philippderroole/RockeyHockey2026/UIServer/resources/gifs/dog.gif

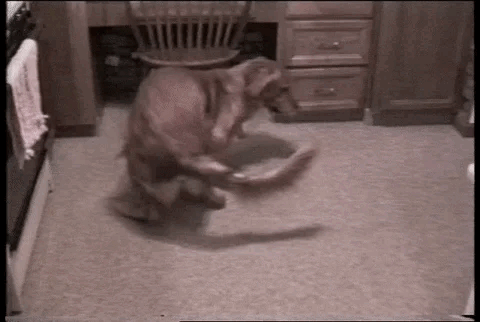
UIServer/resources/gifs/dog.gif
