philippderroole/RockeyHockey2026/CAD/Solidworks/RH_Baugr_Pulley_with_Rail_35mm_X_Axis.SLDASM

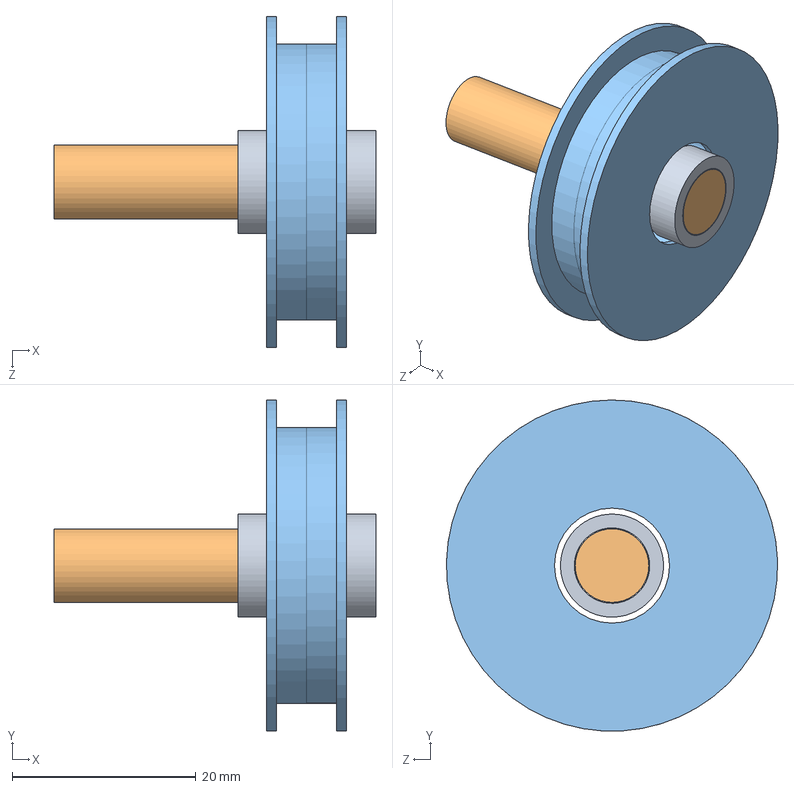
[picture p7: CAD file, 2023-06-27]
CAD/Solidworks/RH_Baugr_Pulley_with_Rail_35mm_X_Axis.SLDASM
35.0 x 36.0 x 36.0 mm
RH_Pulley_36mm_608_GT2_6mm x 2
RH_Rail_8mm_35mm
RH_Spacer_4mm x 2
