philippderroole/RockeyHockey2026/CAD/Solidworks/RH_Baugr_Pulley_with_Rail_24mm_Y_Axis.SLDASM

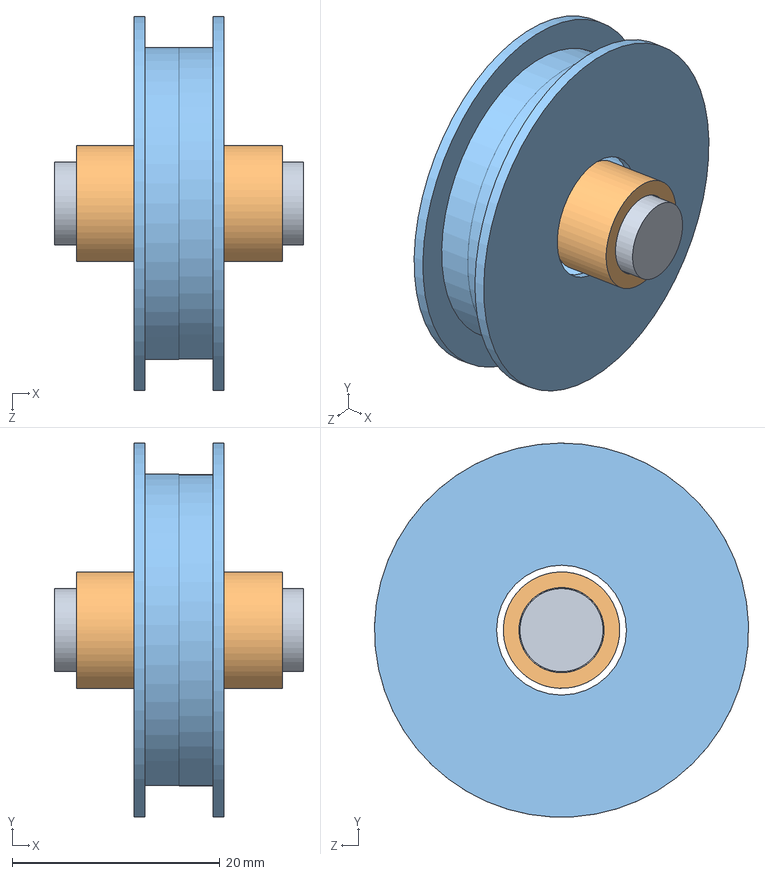
[picture p8: CAD file, 2023-06-27]
CAD/Solidworks/RH_Baugr_Pulley_with_Rail_24mm_Y_Axis.SLDASM
24.0 x 36.0 x 36.0 mm
RH_Pulley_36mm_608_GT2_6mm x 2
RH_Spacer_6_5mm x 2
RH_Rail_8mm_24mm
