philippderroole/RockeyHockey2026/CAD/Solidworks/Rocky_Hockey_Full_Assembly.SLDASM

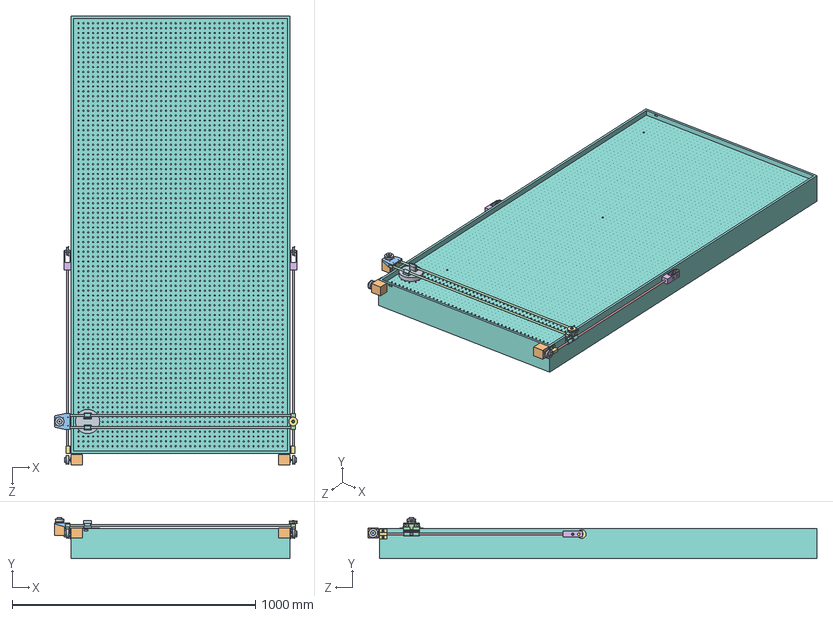
[picture p11: CAD file, 2023-06-27]
CAD/Solidworks/Rocky_Hockey_Full_Assembly.SLDASM
1000.4 x 168.8 x 1847.3 mm
RH_Tisch
RH_Rail_Stopper x 2
RH_Rail_Stopper_with_Pulley x 2
RH_Rail_8mm_770mm x 2
RH_Y_Carriage x 2
RH_Y_Carriage_Motor_Mount
RH_Nema17_Motor x 3
RH_35mm_Riemenscheibe x 3
RH_Bushing_8mm_15mm x 6
RH_Pulley_36mm_608_GT2_6mm x 6
RH_Spacer_6_5mm x 4
RH_Rail_8mm_24mm x 2
RH_Rail_8mm_944_85mm x 2
RH_Rail_8mm_35mm
RH_Spacer_4mm x 2
RH_X_Carriage_Bushings
