philippderroole/RockeyHockey2026/CAD/Solidworks/RH_Nema17_Motor.SLDPRT

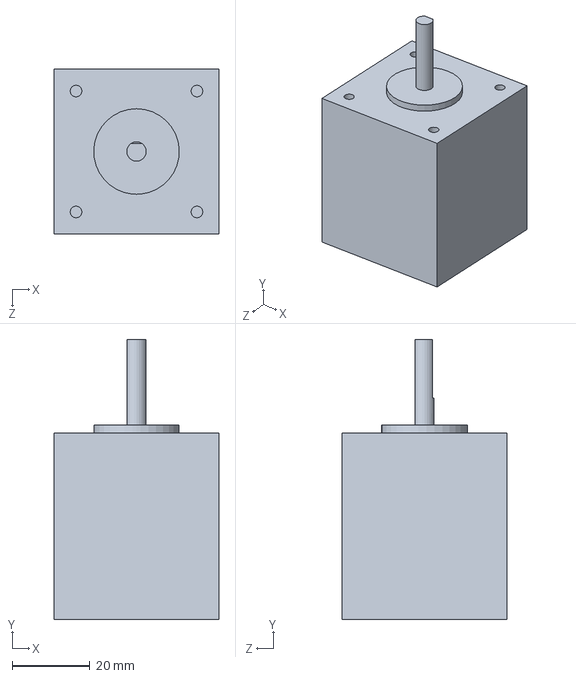
[picture p23: CAD file, 2023-06-27]
CAD/Solidworks/RH_Nema17_Motor.SLDPRT
42.3 x 72.0 x 42.3 mm
