philippderroole/RockeyHockey2026/CAD/STL/X_Carriage_Bushings.STL

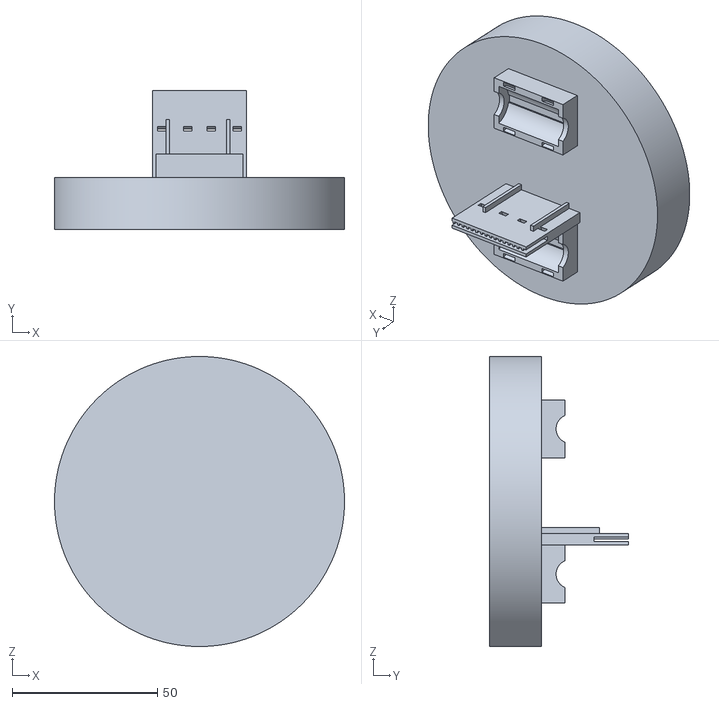
[picture p24: CAD file, 2023-06-27]
CAD/STL/X_Carriage_Bushings.STL
100.0 x 48.0 x 100.0
