philippderroole/RockeyHockey2026/CAD/Solidworks/RH_Rail_Stopper.SLDPRT

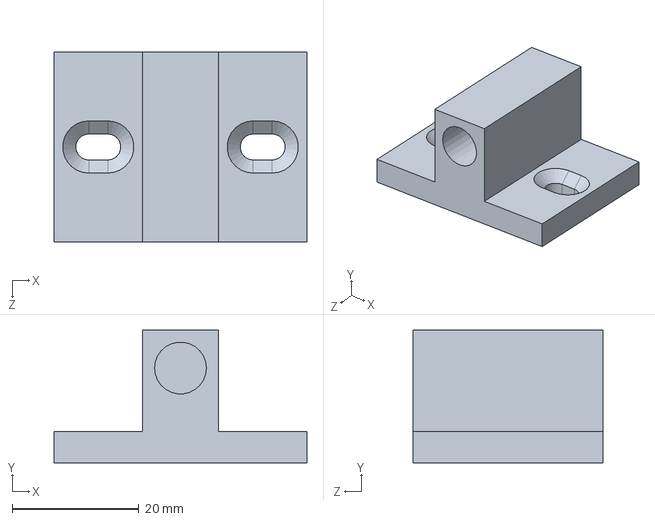
[picture p25: CAD file, 2023-06-27]
CAD/Solidworks/RH_Rail_Stopper.SLDPRT
40.0 x 21.0 x 30.0 mm
