philippderroole/RockeyHockey2026/CAD/STL/Pulley_48_Teeth_GT2_6mm.STL

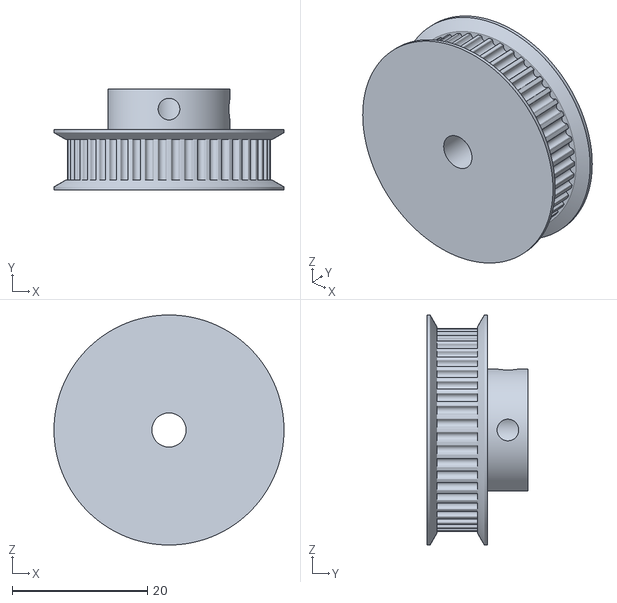
[picture p26: CAD file, 2023-06-27]
CAD/STL/Pulley_48_Teeth_GT2_6mm.STL
34.0 x 15.0 x 34.0
