philippderroole/RockeyHockey2026/CAD/STL/Pulley_42_Teeth_GT2_6mm.STL

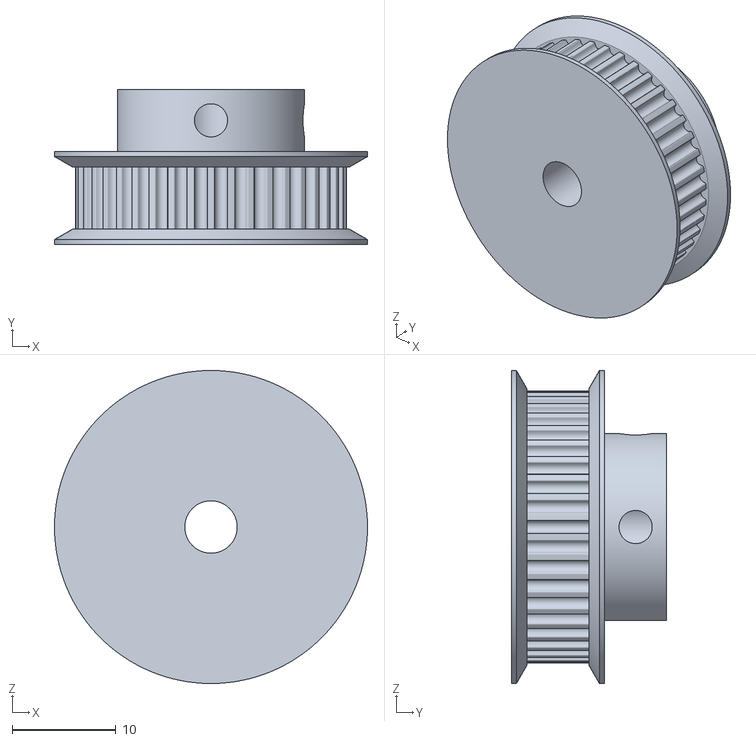
[picture p27: CAD file, 2023-06-27]
CAD/STL/Pulley_42_Teeth_GT2_6mm.STL
30.2 x 15.0 x 30.2
