philippderroole/RockeyHockey2026/CAD/Solidworks/RH_Tisch.SLDPRT

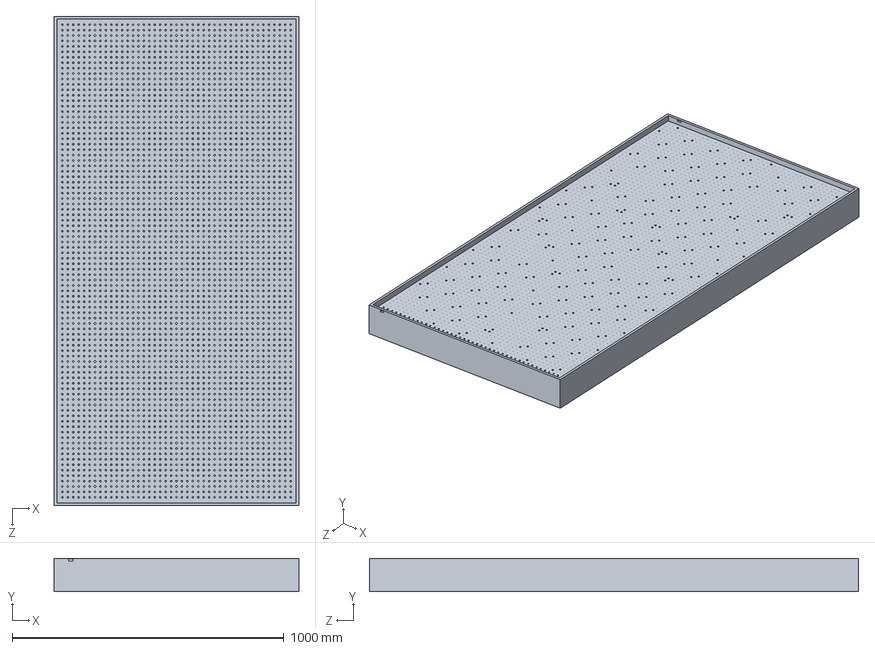
[picture p28: CAD file, 2023-06-27]
CAD/Solidworks/RH_Tisch.SLDPRT
900.0 x 122.5 x 1800.0 mm
