philippderroole/RockeyHockey2026/CAD/STL/Pulley_36mm_608_GT2_6mm.STL

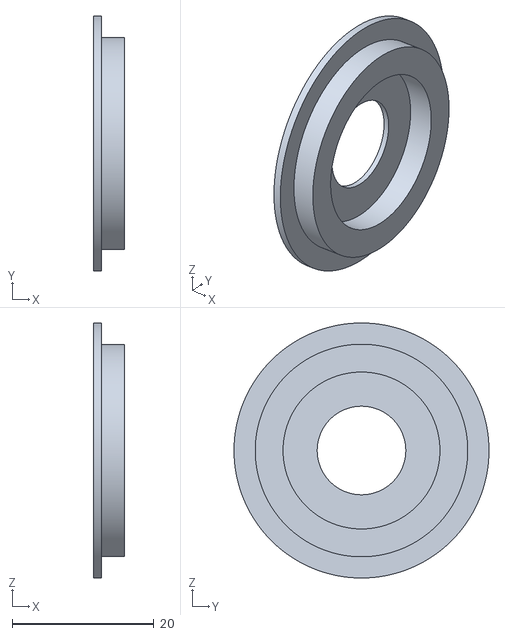
[picture p29: CAD file, 2023-06-27]
CAD/STL/Pulley_36mm_608_GT2_6mm.STL
4.35 x 36.0 x 36.0
