philippderroole/RockeyHockey2026/CAD/Solidworks/RH_Spacer_6_5mm.SLDPRT

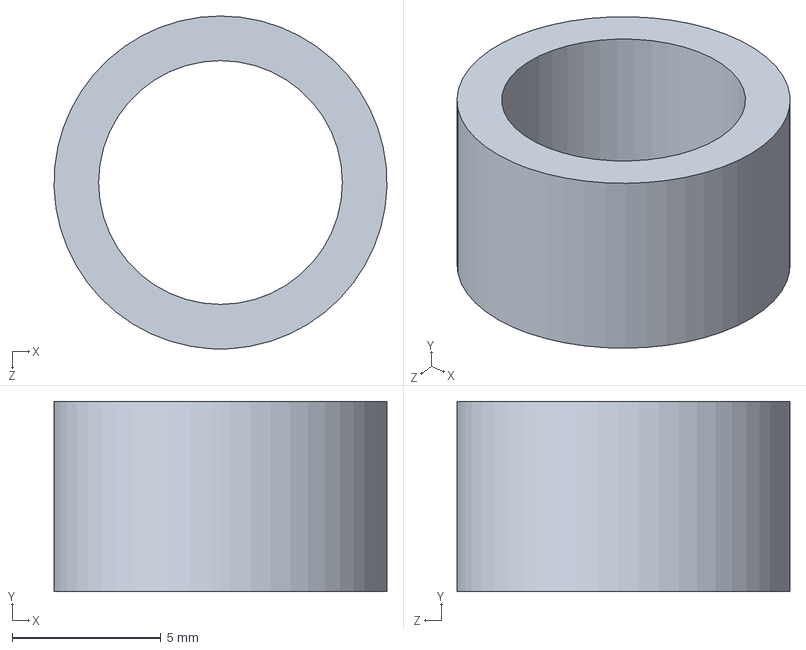
[picture p30: CAD file, 2023-06-27]
CAD/Solidworks/RH_Spacer_6_5mm.SLDPRT
11.2 x 6.40 x 11.2 mm
