philippderroole/RockeyHockey2026/CAD/Solidworks/RH_Rail_8mm_944_85mm.SLDPRT

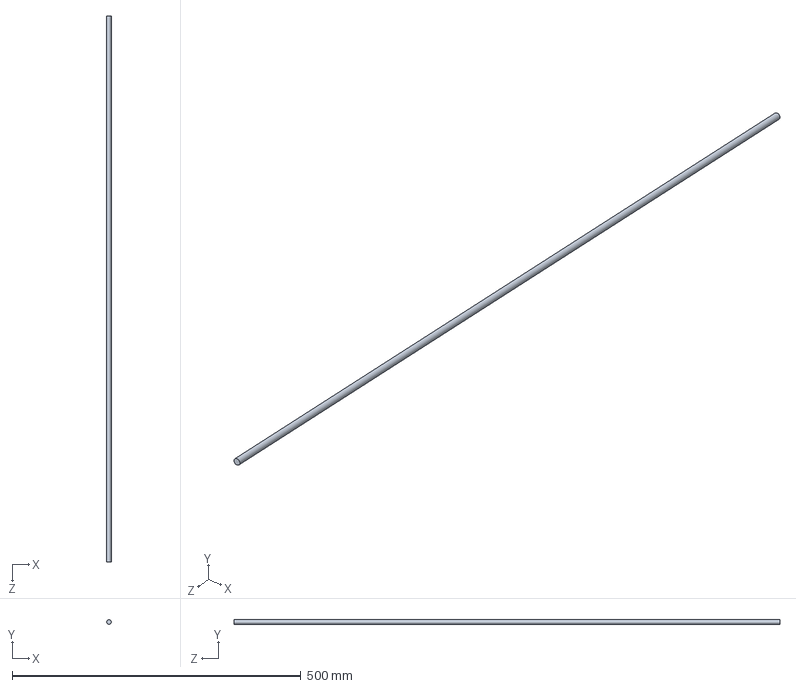
[picture p31: CAD file, 2023-06-27]
CAD/Solidworks/RH_Rail_8mm_944_85mm.SLDPRT
8.00 x 8.00 x 944.9 mm
