philippderroole/RockeyHockey2026/CAD/Solidworks/RH_Rail_8mm_770mm.SLDPRT

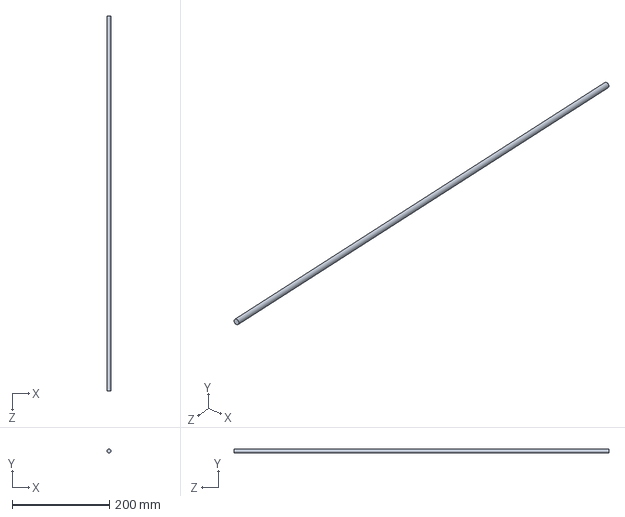
[picture p32: CAD file, 2023-06-27]
CAD/Solidworks/RH_Rail_8mm_770mm.SLDPRT
8.00 x 8.00 x 770.0 mm
