philippderroole/RockeyHockey2026/CAD/Solidworks/RH_Spacer_4mm.SLDPRT

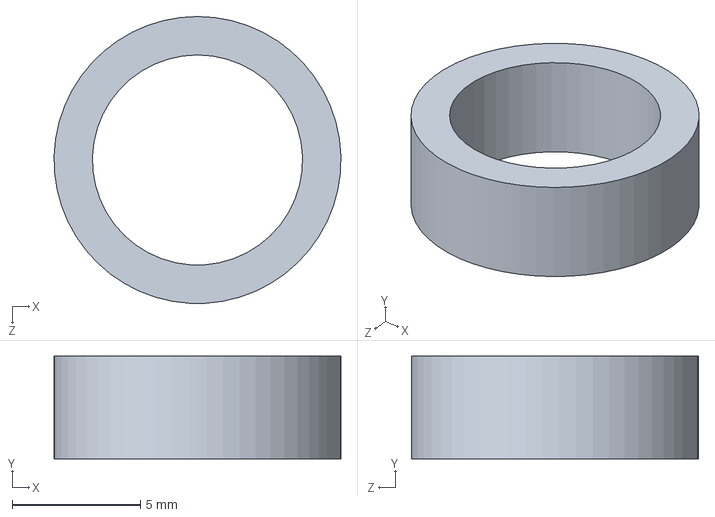
[picture p33: CAD file, 2023-06-27]
CAD/Solidworks/RH_Spacer_4mm.SLDPRT
11.2 x 4.00 x 11.2 mm
