philippderroole/RockeyHockey2026/Strategy/src/strategy.rs

use nalgebra::Point2;

use crate::{
    commands::Command,
    config::{
        BOARD_HEIGHT, BOARD_WIDTH, GOAL_Y_MAX, GOAL_Y_MIN, LEFT_BORDER_REPOSITION_X,
        PLAYABLE_PUCK_THRESHOLD, PUCK_RADIUS, RESTING_PUCK_THRESHOLD, ROBOT_ATTACK_MAX_X,
        ROBOT_DEFENSE_MAX_Y, ROBOT_DEFENSE_MIN_Y, ROBOT_MAX_X, ROBOT_MAX_Y,
    },
    puck::Puck,
    simulation::predict_puck_path,
};

const ATTACK_STAGING_DISTANCE: f64 = 50.0;

pub fn get_next_move(_robot_pos: Point2<f64>, puck: &Puck) -> (Option<Command>, Vec<Point2<f64>>) {
    let predicted_puck_path = predict_puck_path(puck);

    let new_target = if puck_at_left_border(puck)
        && puck.velocity().magnitude() >= RESTING_PUCK_THRESHOLD
    {
        None
    } else if let Some(goal_block_target) = goal_block_target(&predicted_puck_path) {
        Some(goal_block_target)
    } else if puck_at_left_border(puck) {
        left_boarder_defense(puck)
    } else if puck.velocity().magnitude() < PLAYABLE_PUCK_THRESHOLD && puck.x() < ROBOT_ATTACK_MAX_X
    {
        attack_target(puck)
    } else {
        Some(Command::MoveTo(Point2::new(10.0, ROBOT_MAX_Y * 0.5)))
    };

    (new_target, predicted_puck_path)
}

fn goal_block_target(predicted_puck_path: &[Point2<f64>]) -> Option<Command> {
    predicted_puck_path
        .iter()
        .find(|point| point.x <= PUCK_RADIUS && point.y >= GOAL_Y_MIN && point.y <= GOAL_Y_MAX)
        .map(|point| {
            Command::Defend(Point2::new(
                10.0,
                point.y.clamp(ROBOT_DEFENSE_MIN_Y, ROBOT_DEFENSE_MAX_Y),
            ))
        })
}

fn attack_target(puck: &Puck) -> Option<Command> {
    let puck_position = Point2::new(puck.x(), puck.y());
    let goal_center = Point2::new(BOARD_HEIGHT, (GOAL_Y_MIN + GOAL_Y_MAX) * 0.5);
    let aim_point = preferred_attack_aim_point(puck_position, goal_center);
    let staging_target = attack_staging_target(puck_position, aim_point);

    Some(Command::Shoot {
        staging: staging_target,
        target: overshoot_target(puck_position, aim_point),
    })
}

fn attack_staging_target(puck_position: Point2<f64>, aim_point: Point2<f64>) -> Point2<f64> {
    let shot_vector = aim_point - puck_position;
    let shot_distance = shot_vector.magnitude();
    if shot_distance <= f64::EPSILON {
        return puck_position;
    }

    let staging_position = puck_position - shot_vector / shot_distance * ATTACK_STAGING_DISTANCE;

    Point2::new(
        staging_position.x.clamp(0.0, ROBOT_MAX_X),
        staging_position.y.clamp(0.0, ROBOT_MAX_Y),
    )
}

fn preferred_attack_aim_point(puck_position: Point2<f64>, goal_center: Point2<f64>) -> Point2<f64> {
    let top_bank = Point2::new(goal_center.x, -goal_center.y);
    let bottom_bank = Point2::new(goal_center.x, BOARD_WIDTH * 2.0 - goal_center.y);

    let top_bounce_x = wall_bounce_x(puck_position, top_bank, 0.0);
    let bottom_bounce_x = wall_bounce_x(puck_position, bottom_bank, BOARD_WIDTH);

    let top_bounce_is_safe = top_bounce_x
        .map(|x| (PUCK_RADIUS..=BOARD_HEIGHT - PUCK_RADIUS).contains(&x))
        .unwrap_or(false);
    let bottom_bounce_is_safe = bottom_bounce_x
        .map(|x| (PUCK_RADIUS..=BOARD_HEIGHT - PUCK_RADIUS).contains(&x))
        .unwrap_or(false);

    match (top_bounce_is_safe, bottom_bounce_is_safe) {
        (true, false) => top_bank,
        (false, true) => bottom_bank,
        (true, true) => {
            if puck_position.y < BOARD_WIDTH * 0.5 {
                top_bank
            } else {
                bottom_bank
            }
        }
        (false, false) => goal_center,
    }
}

fn wall_bounce_x(puck_position: Point2<f64>, aim_point: Point2<f64>, wall_y: f64) -> Option<f64> {
    let delta_y = aim_point.y - puck_position.y;
    if delta_y.abs() <= f64::EPSILON {
        return None;
    }

    let t = (wall_y - puck_position.y) / delta_y;
    if !(0.0..=1.0).contains(&t) {
        return None;
    }

    Some(puck_position.x + (aim_point.x - puck_position.x) * t)
}

fn overshoot_target(puck_position: Point2<f64>, aim_point: Point2<f64>) -> Point2<f64> {
    let shot_vector = aim_point - puck_position;
    let shot_distance = shot_vector.magnitude();
    if shot_distance <= f64::EPSILON {
        return puck_position;
    }

    let overshoot_distance = (PUCK_RADIUS * 2.5).max(40.0);
    let overshoot_position = puck_position + shot_vector / shot_distance * overshoot_distance;

    Point2::new(
        overshoot_position.x.clamp(0.0, ROBOT_MAX_X),
        overshoot_position.y.clamp(0.0, ROBOT_MAX_Y),
    )
}

fn puck_at_left_border(puck: &Puck) -> bool {
    puck.x() < LEFT_BORDER_REPOSITION_X
}

fn left_boarder_defense(puck: &Puck) -> Option<Command> {
    if puck.x() < LEFT_BORDER_REPOSITION_X {
        Some(Command::Defend(Point2::new(
            10.0,
            puck.y().clamp(ROBOT_DEFENSE_MIN_Y, ROBOT_DEFENSE_MAX_Y),
        )))
    } else {
        None
    }
}
